Li-Mingshuang/flipdeck/out/contact_sheet.png

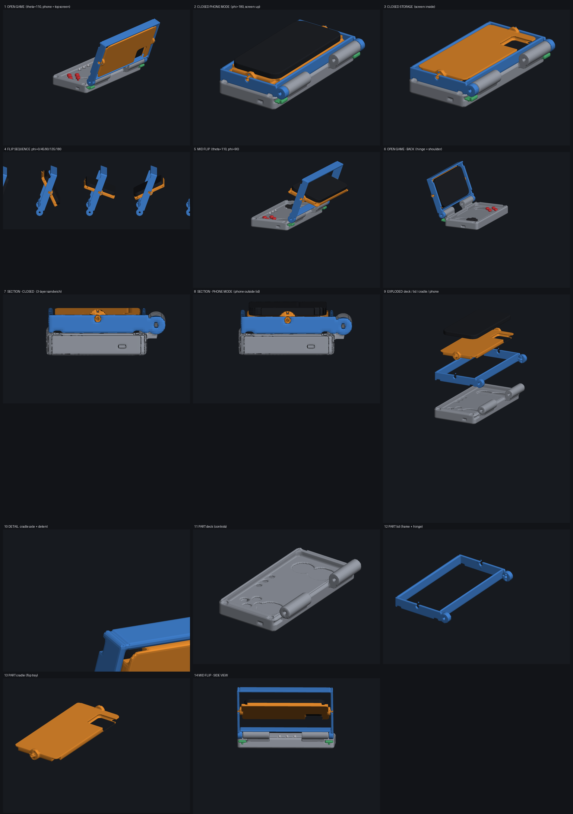
out/contact_sheet.png
