Li-Mingshuang/flipdeck/out/ip12/part_cradle.png

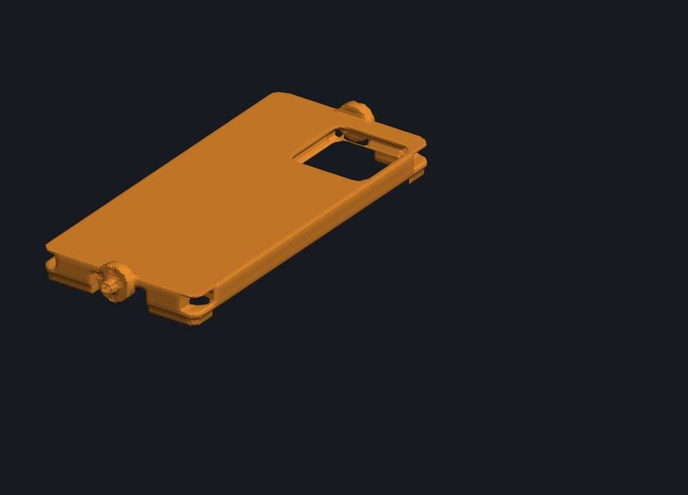
out/ip12/part_cradle.png
