Li-Mingshuang/flipdeck/out/ip12/part_deck.png

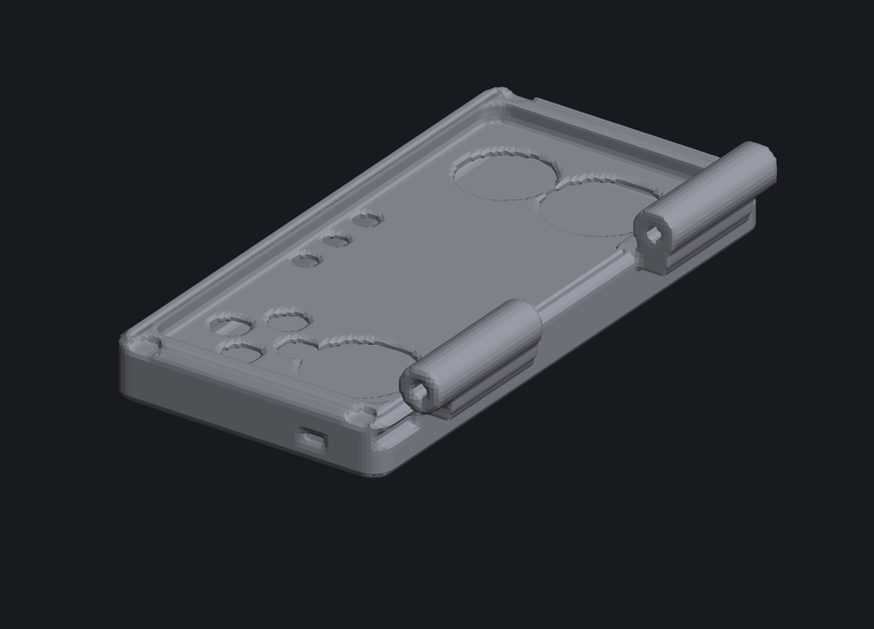
out/ip12/part_deck.png
