Li-Mingshuang/flipdeck/out/ip12/part_lid.png

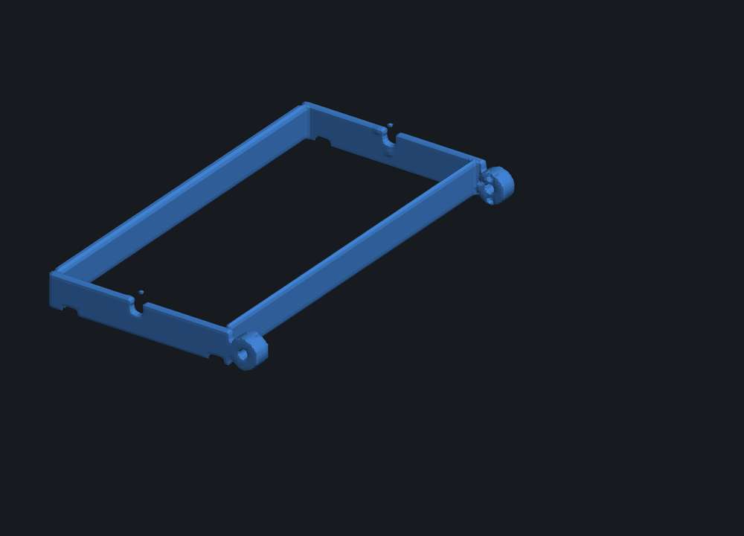
out/ip12/part_lid.png
