Li-Mingshuang/flipdeck/out/ip12/render_closed_game.png

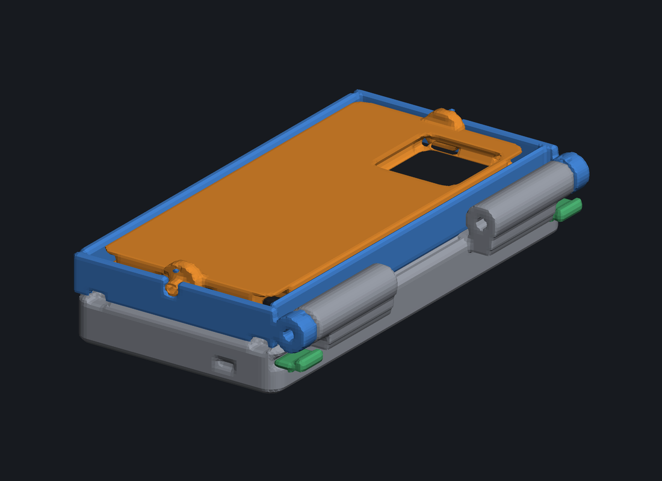
out/ip12/render_closed_game.png
