Li-Mingshuang/flipdeck/out/ip12/render_closed_phone.png

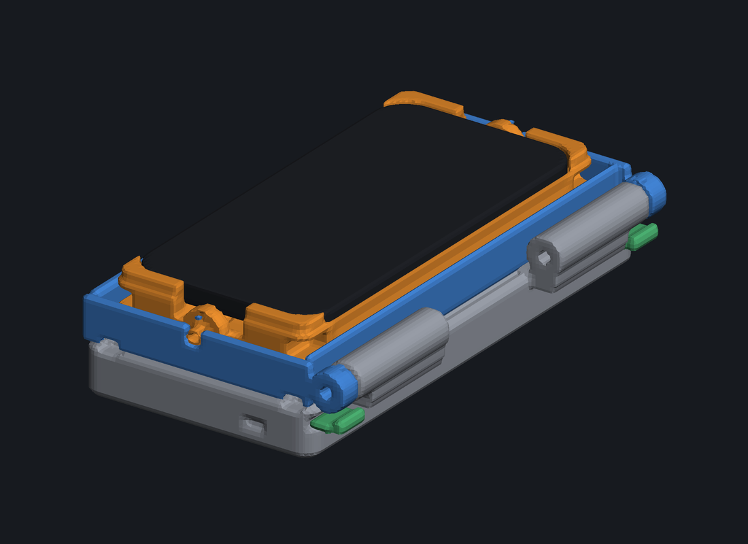
out/ip12/render_closed_phone.png
