Li-Mingshuang/flipdeck/out/ip12/render_detail_axle.png

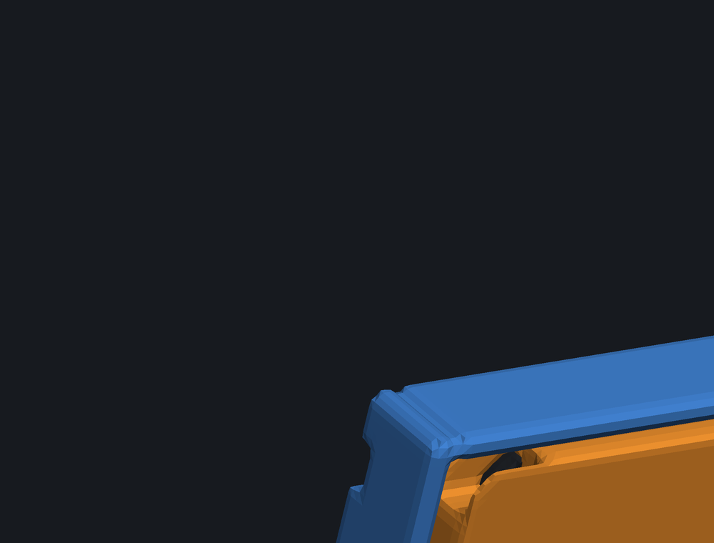
out/ip12/render_detail_axle.png
