Li-Mingshuang/flipdeck/out/ip12/render_flip_sequence.png

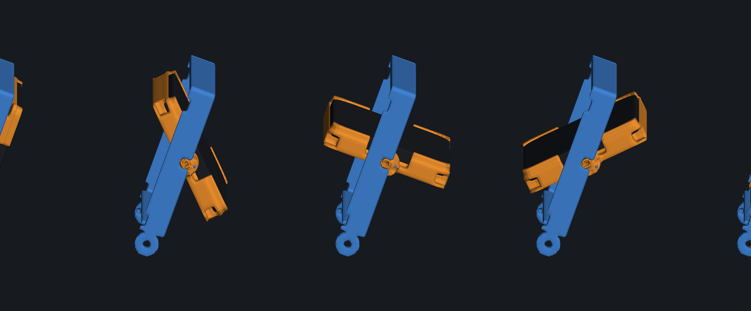
out/ip12/render_flip_sequence.png
