Li-Mingshuang/flipdeck/out/ip12/render_section_closed.png

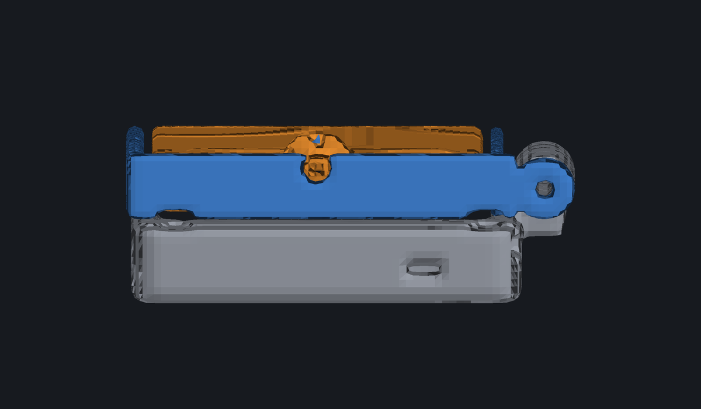
out/ip12/render_section_closed.png
