Li-Mingshuang/flipdeck/out/ip12/render_switch_mid.png

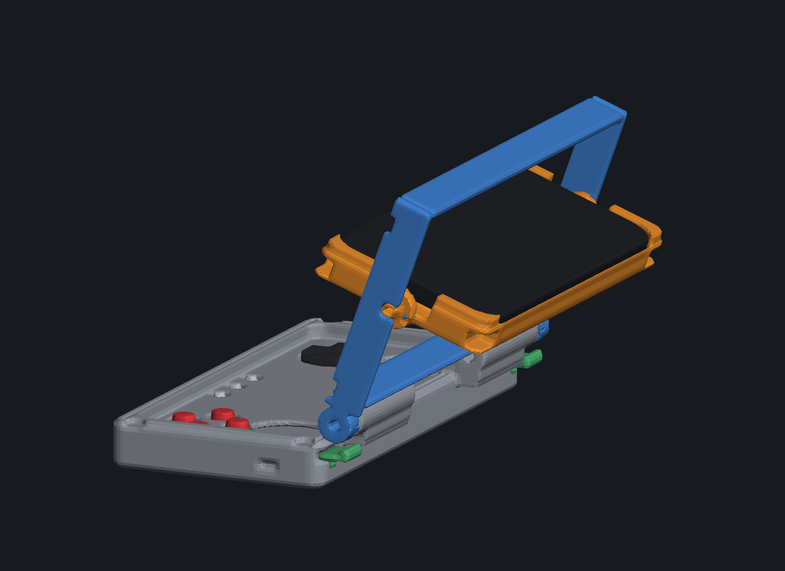
out/ip12/render_switch_mid.png
