Li-Mingshuang/flipdeck/out/ip12/render_switch_mid_side.png

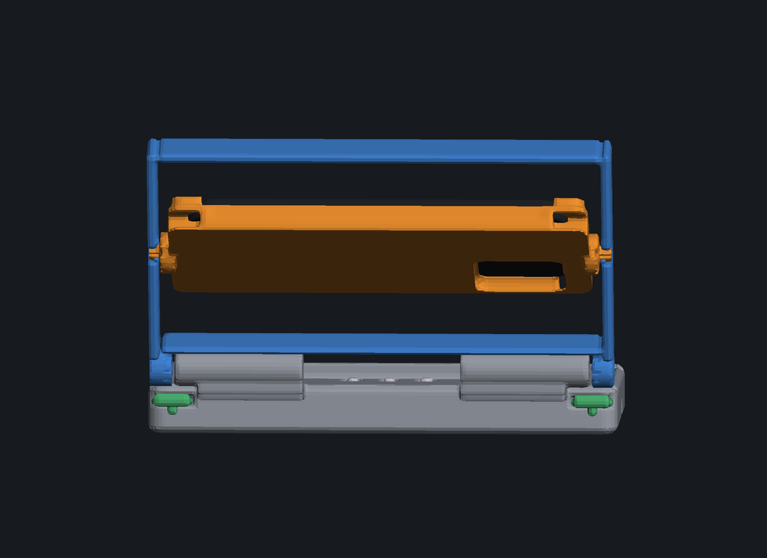
out/ip12/render_switch_mid_side.png
