Li-Mingshuang/flipdeck/out/pcb/flipdeck_pcb_layout.png

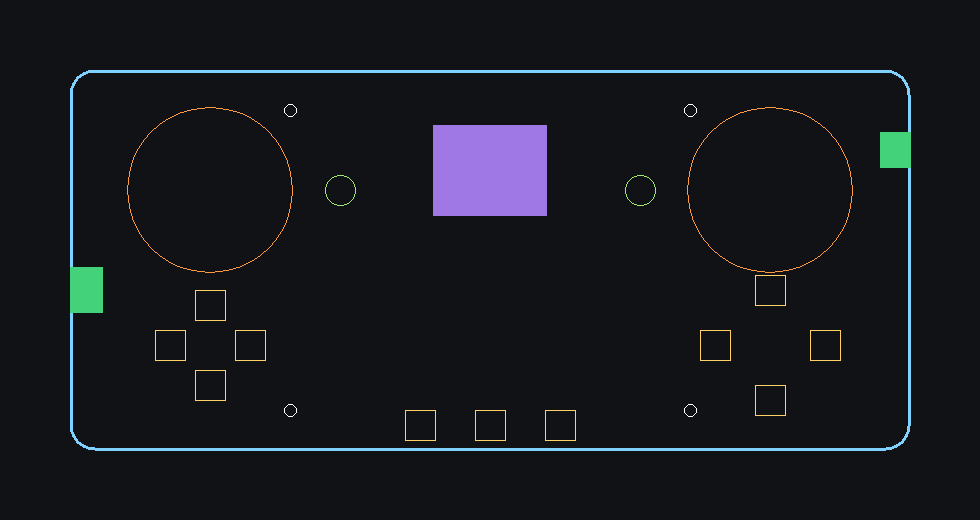
out/pcb/flipdeck_pcb_layout.png
