Li-Mingshuang/flipdeck/out/render_closed_game.png

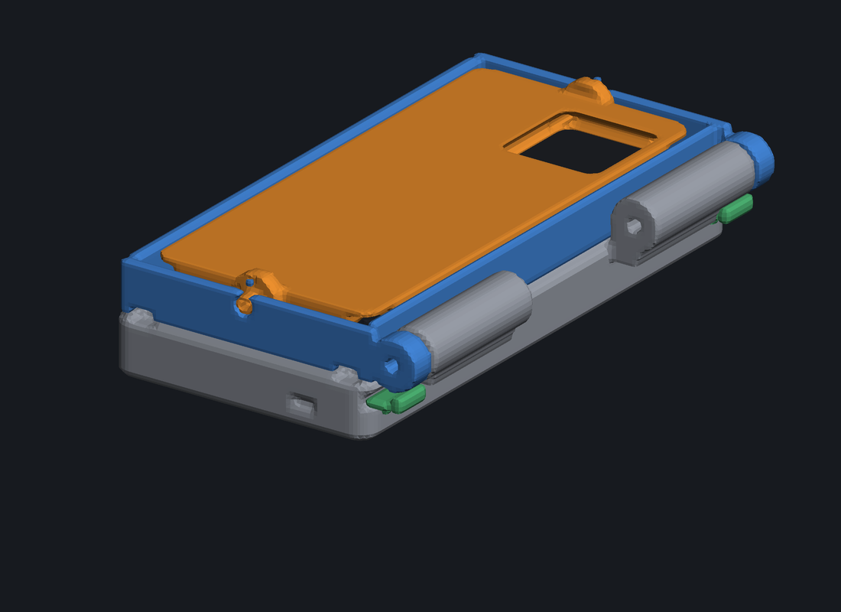
out/render_closed_game.png
