Li-Mingshuang/flipdeck/out/render_closed_phone.png

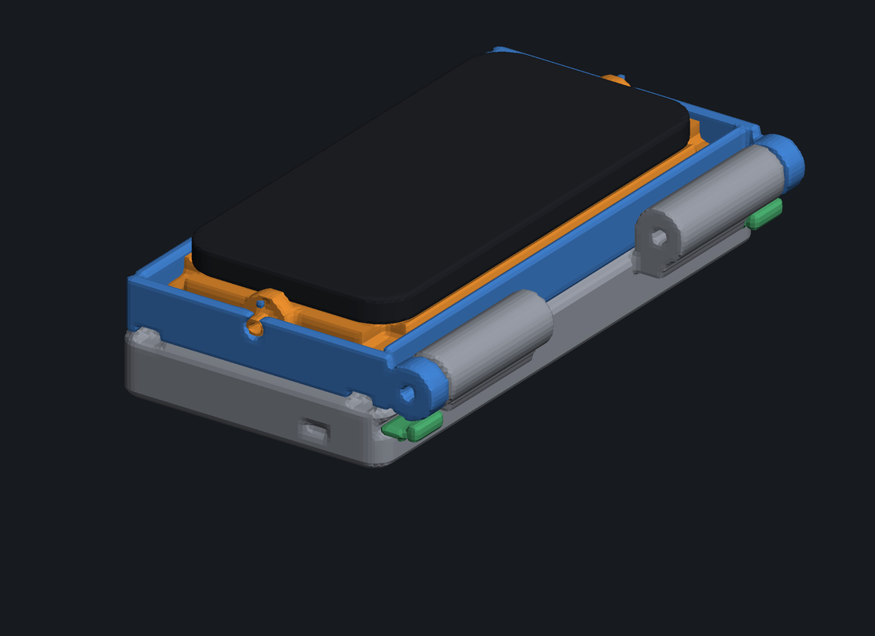
out/render_closed_phone.png
