Li-Mingshuang/flipdeck/out/render_exploded.png

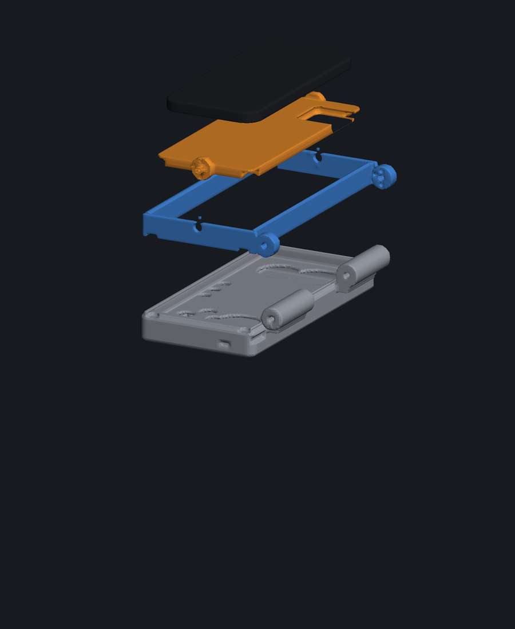
out/render_exploded.png
