Li-Mingshuang/flipdeck/out/render_open_game.png

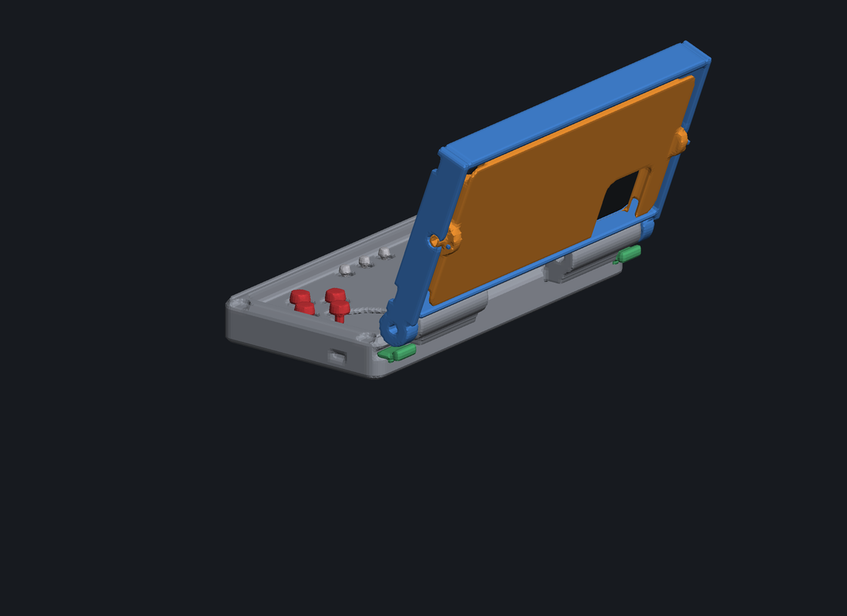
out/render_open_game.png
