Li-Mingshuang/flipdeck/out/render_open_game_back.png

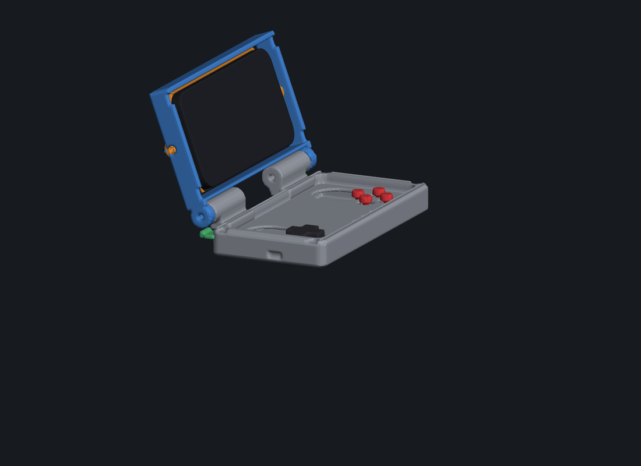
out/render_open_game_back.png
