Li-Mingshuang/flipdeck/out/render_section_phone.png

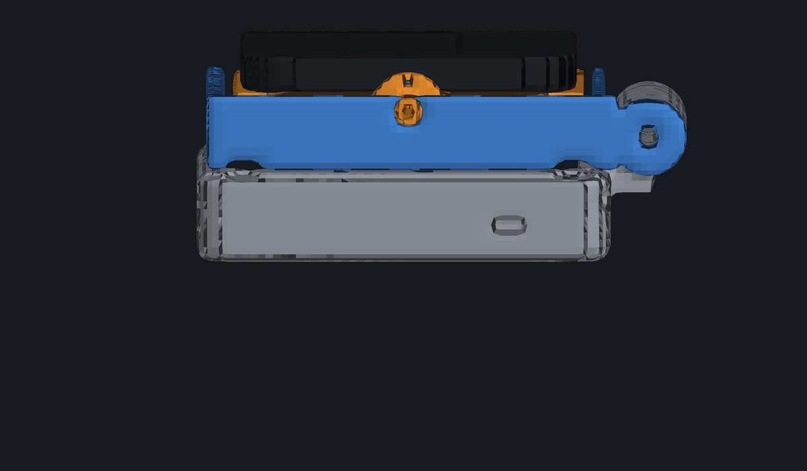
out/render_section_phone.png
