Li-Mingshuang/flipdeck/docs/stl/lever_r.stl

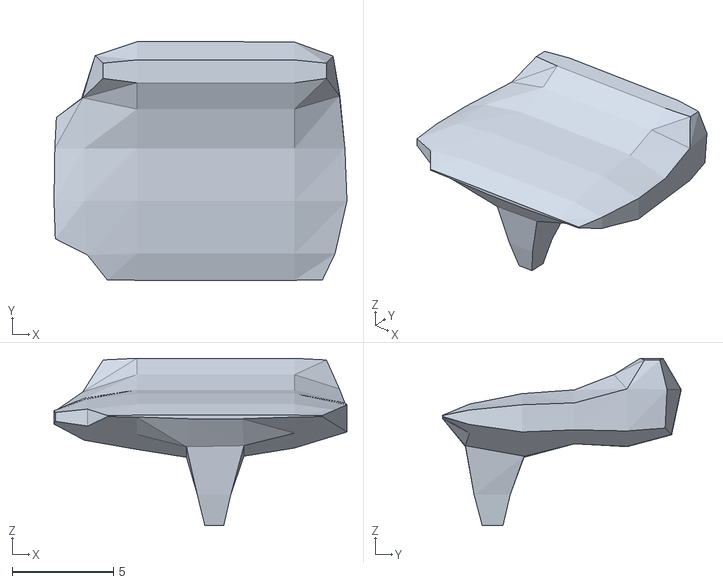
[picture p36: CAD file, 2026-09-13]
docs/stl/lever_r.stl
14.5 x 11.8 x 8.28
