Li-Mingshuang/flipdeck/out/stl/caps_small.stl

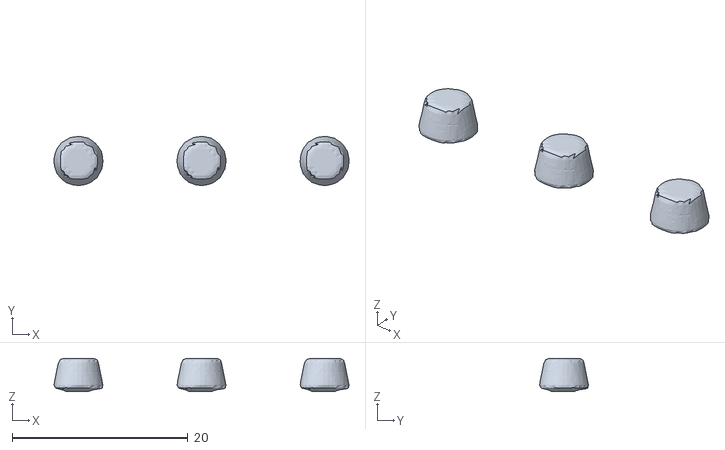
[picture p37: CAD file, 2026-09-13]
out/stl/caps_small.stl
33.6 x 5.56 x 3.80
