Li-Mingshuang/flipdeck/web/stl/cap_y.stl

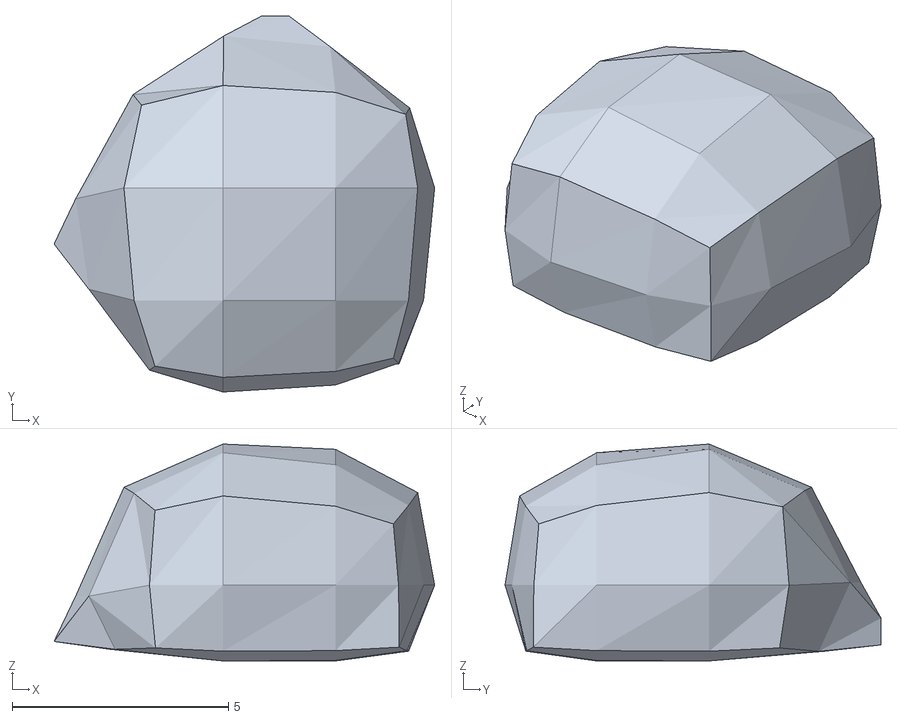
[picture p38: CAD file, 2026-09-13]
web/stl/cap_y.stl
8.80 x 8.70 x 5.02
