Li-Mingshuang/flipdeck/docs/stl/cap_start.stl

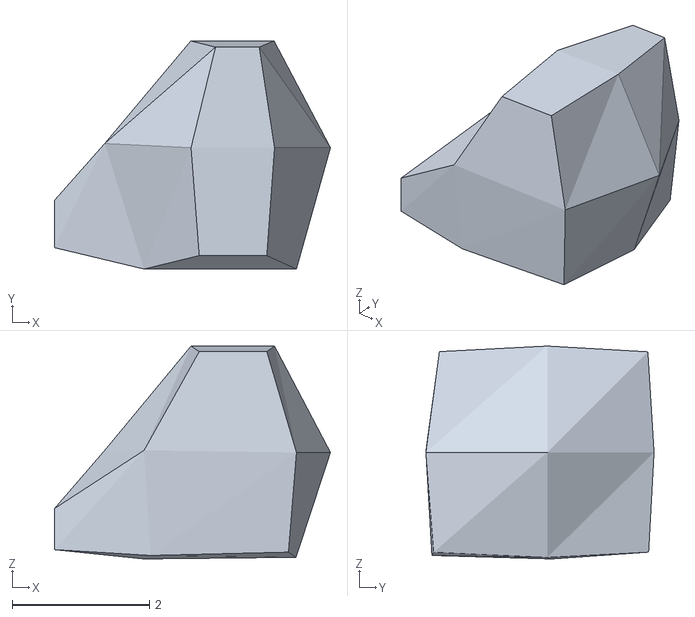
[picture p39: CAD file, 2026-09-13]
docs/stl/cap_start.stl
4.02 x 3.32 x 3.10
