Li-Mingshuang/flipdeck/web/stl/cap_x.stl

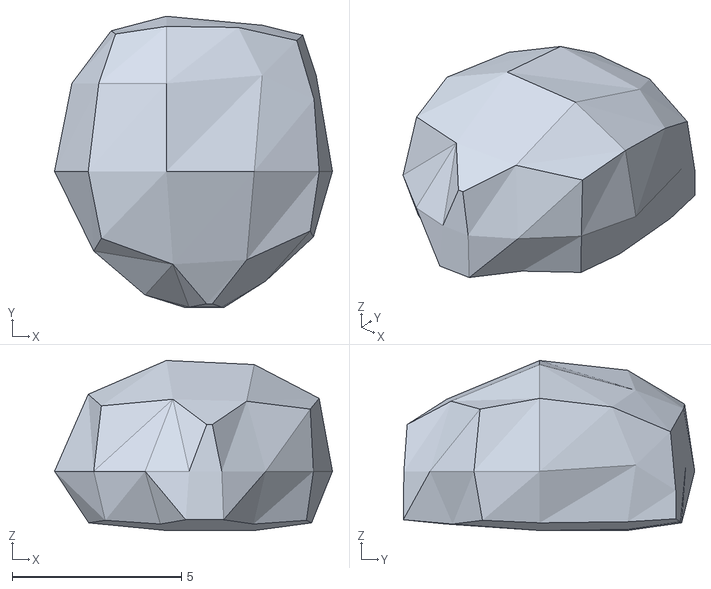
[picture p40: CAD file, 2026-09-13]
web/stl/cap_x.stl
8.22 x 8.62 x 5.03
