Li-Mingshuang/flipdeck/docs/stl/cap_b.stl

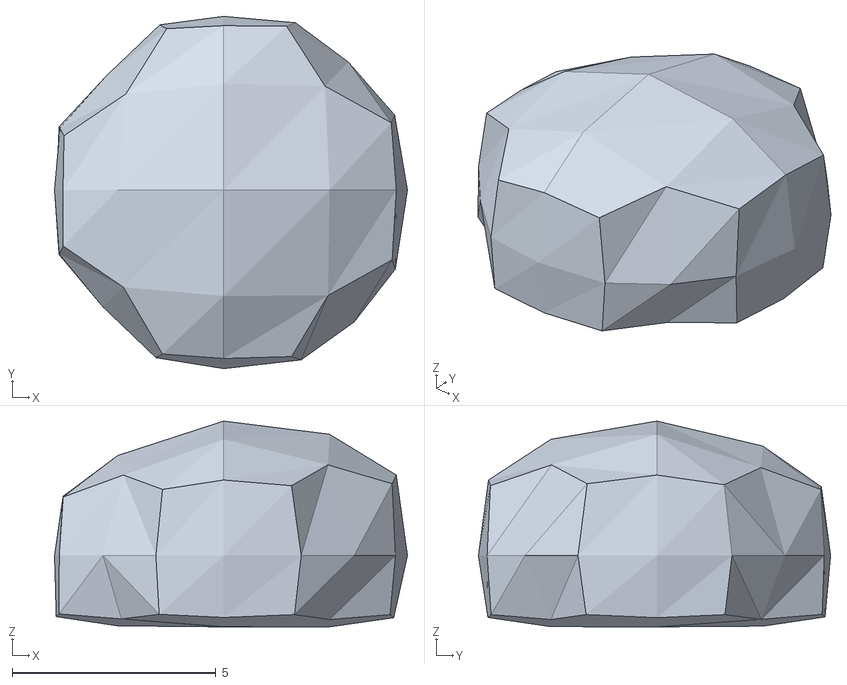
[picture p41: CAD file, 2026-09-13]
docs/stl/cap_b.stl
8.66 x 8.65 x 5.05
