Li-Mingshuang/flipdeck/docs/stl/stick_l_cap.stl

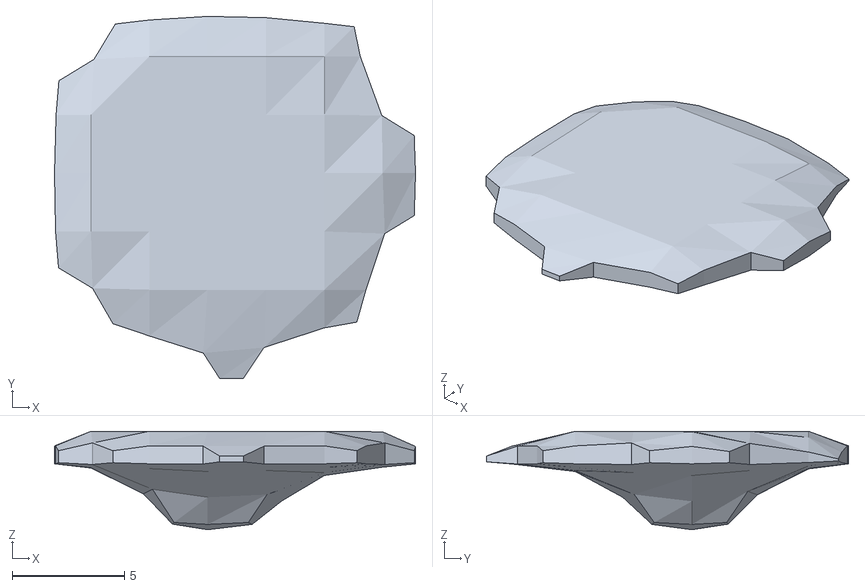
[picture p42: CAD file, 2026-09-13]
docs/stl/stick_l_cap.stl
16.1 x 16.1 x 4.39
