Li-Mingshuang/flipdeck/web/stl/cap_select.stl

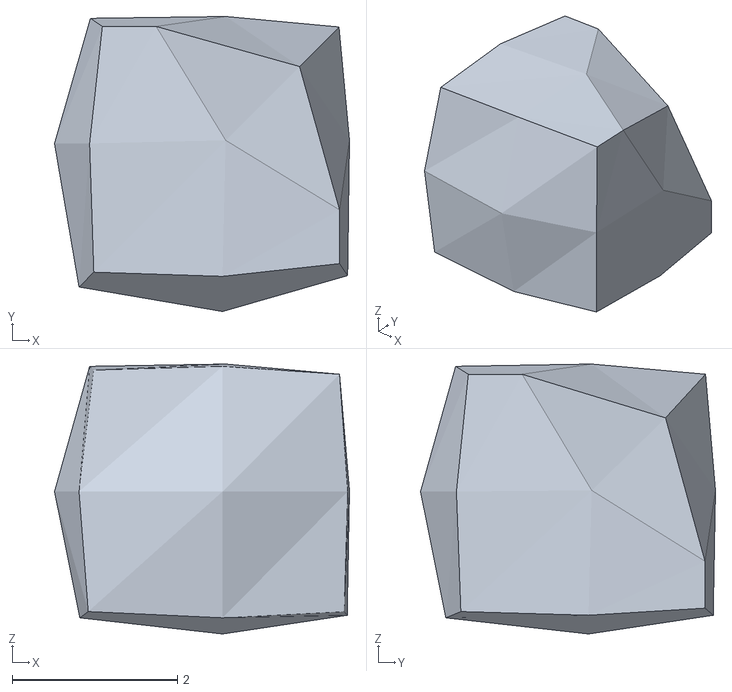
[picture p43: CAD file, 2026-09-13]
web/stl/cap_select.stl
3.57 x 3.57 x 3.26
