Li-Mingshuang/flipdeck/docs/stl/cap_home.stl

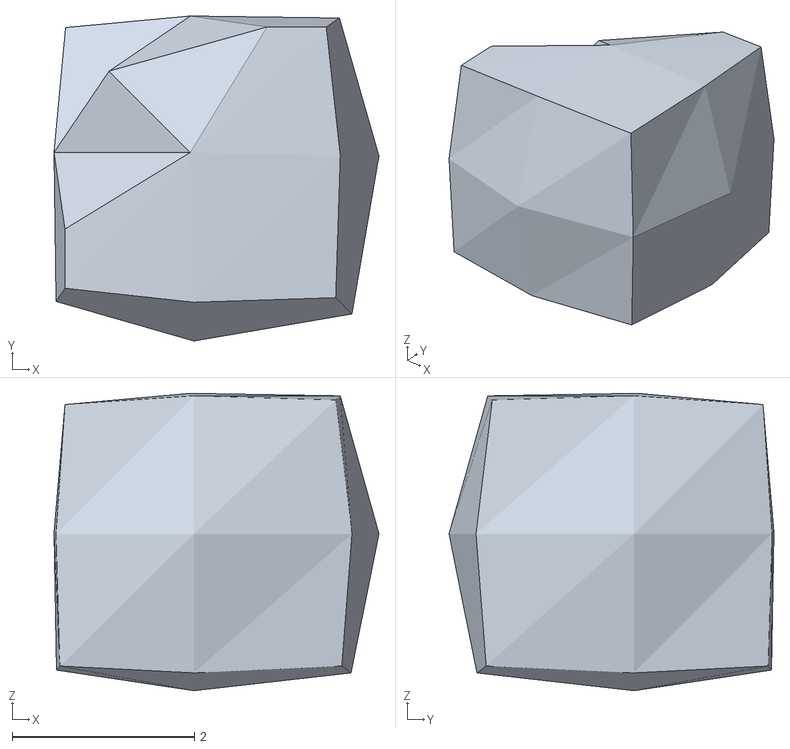
[picture p44: CAD file, 2026-09-13]
docs/stl/cap_home.stl
3.57 x 3.57 x 3.26
