Li-Mingshuang/flipdeck/docs/stl/stick_r_cap.stl

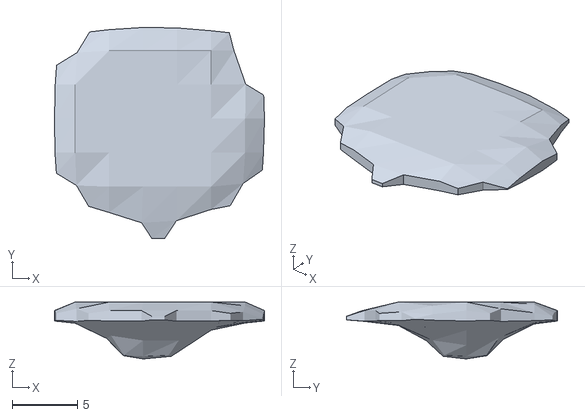
[picture p45: CAD file, 2026-09-13]
docs/stl/stick_r_cap.stl
16.1 x 16.1 x 4.35
