Li-Mingshuang/flipdeck/web/stl/sticks_base.stl

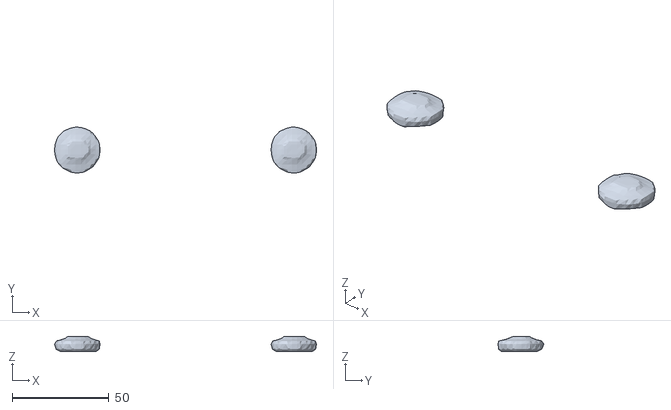
[picture p46: CAD file, 2026-09-13]
web/stl/sticks_base.stl
135.5 x 23.7 x 8.00
