Li-Mingshuang/flipdeck/docs/stl/lever_l.stl

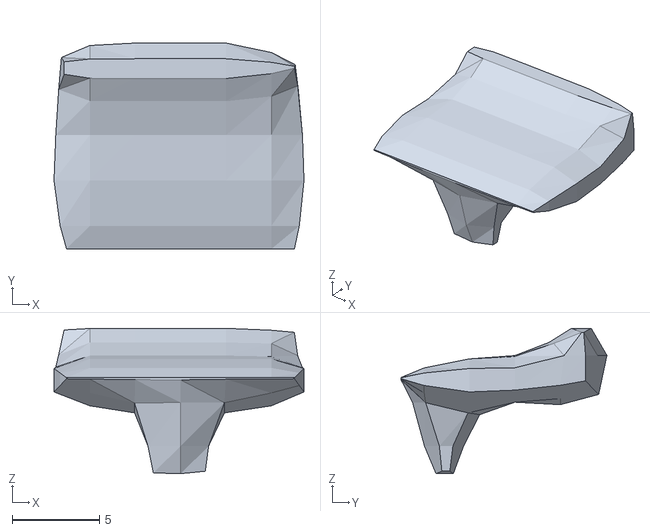
[picture p47: CAD file, 2026-09-13]
docs/stl/lever_l.stl
14.3 x 11.8 x 8.33
