Li-Mingshuang/flipdeck/web/stl/cap_a.stl

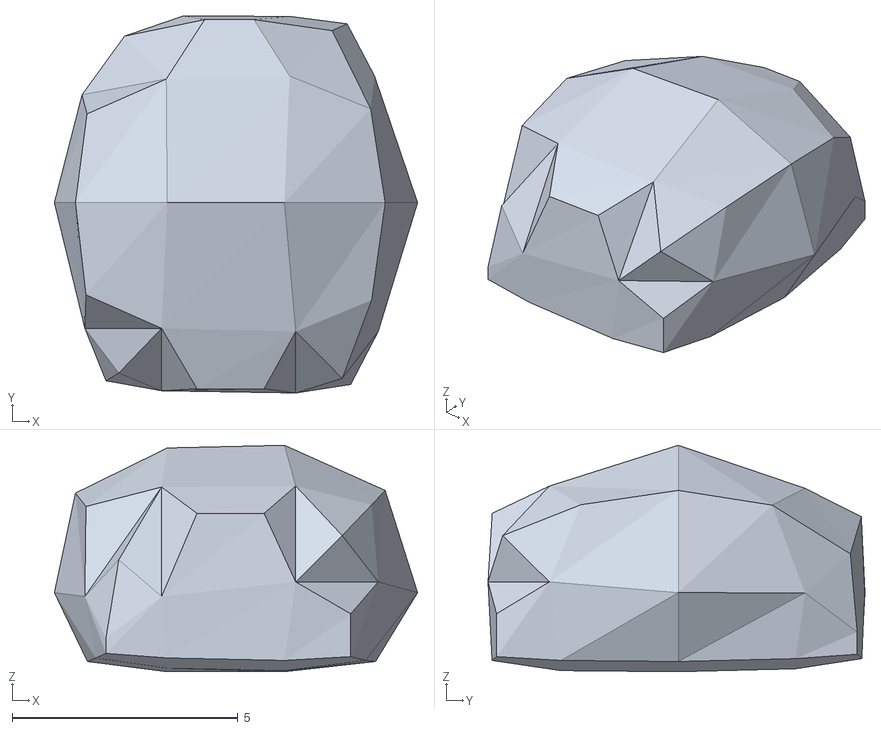
[picture p48: CAD file, 2026-09-13]
web/stl/cap_a.stl
8.05 x 8.36 x 5.02
