Li-Mingshuang/flipdeck/docs/stl/cap_dpad.stl

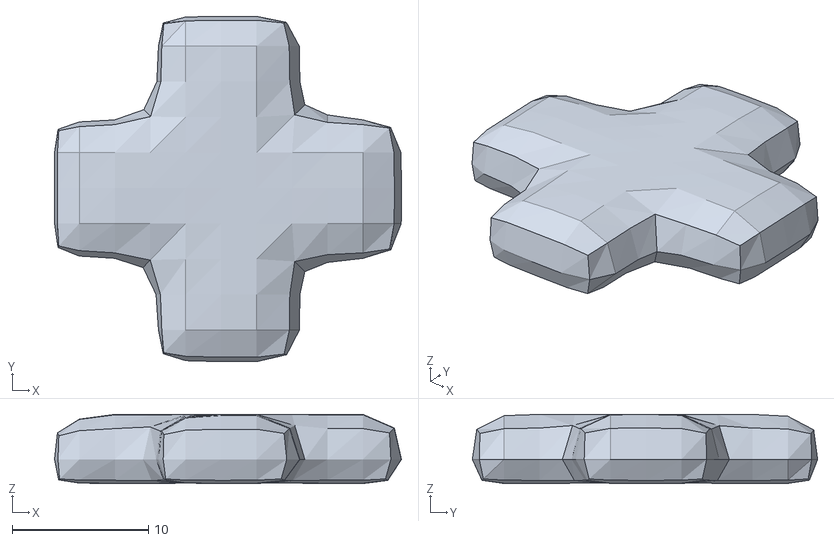
[picture p49: CAD file, 2026-09-13]
docs/stl/cap_dpad.stl
25.4 x 25.3 x 5.07
